MaysaraHolmes/beehive/src/system/Fan.cpp

#include "Fan.hpp"


Fan* Fan::saved_Fan_pointer = NULL;

Fan::Fan(int gpio, int interruptPin){
  setFanPointer();
	this->gpio = gpio;
  this->interruptPin = interruptPin;
  wiringPiSetupGpio();
  pinMode(this->gpio, PWM_OUTPUT);
  pinMode(22, INPUT);
  int state = wiringPiISR(this->interruptPin, INT_EDGE_BOTH, onInterrupt);
}

void Fan::setFanPointer(){
	this->saved_Fan_pointer = this;
}

void Fan::setPwm(int pwm_value){
  pwmWrite(this->gpio, pwm_value);
}

void Fan::start(){
  pwmWrite(this->gpio, 1023);
}

void Fan::stop(){
  pwmWrite(this->gpio, 0);
}

void Fan::onInterrupt(){
  if (digitalRead(saved_Fan_pointer->interruptPin) == HIGH){
    saved_Fan_pointer->start();
  }
  else{
    saved_Fan_pointer->stop();
  }
}

Fan::~Fan(){
  this->stop();
}
